vhs/tacos-esp-integrated/include/cert-auth-cert.h

#ifndef CERT_AUTH_CERT_H
#define CERT_AUTH_CERT_H

#include <Arduino.h>

static const char certauthcert[] PROGMEM = R"EOF(
-----BEGIN CERTIFICATE-----
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
-----END CERTIFICATE-----
)EOF";

#endif
